UBCRapid/Robin-Platform/Documentation/System diagram.PNG

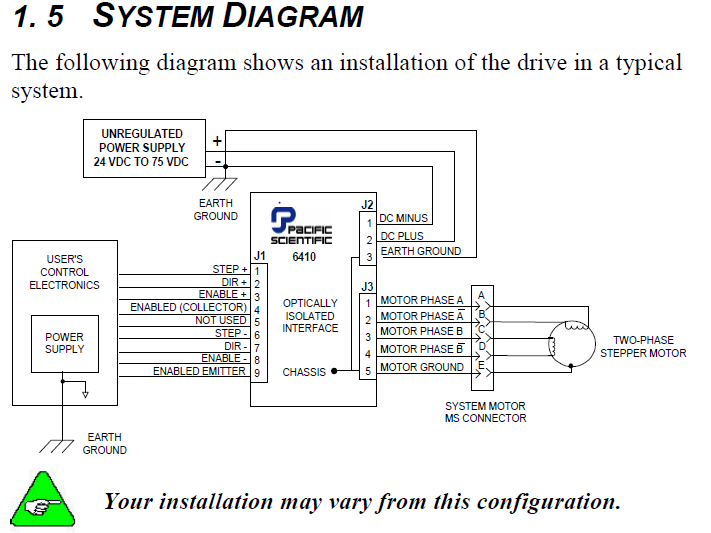
Documentation/System diagram.PNG
