UBCRapid/Robin-Platform/Encoder and Limit Pics/IMG_20140217_170500.jpg

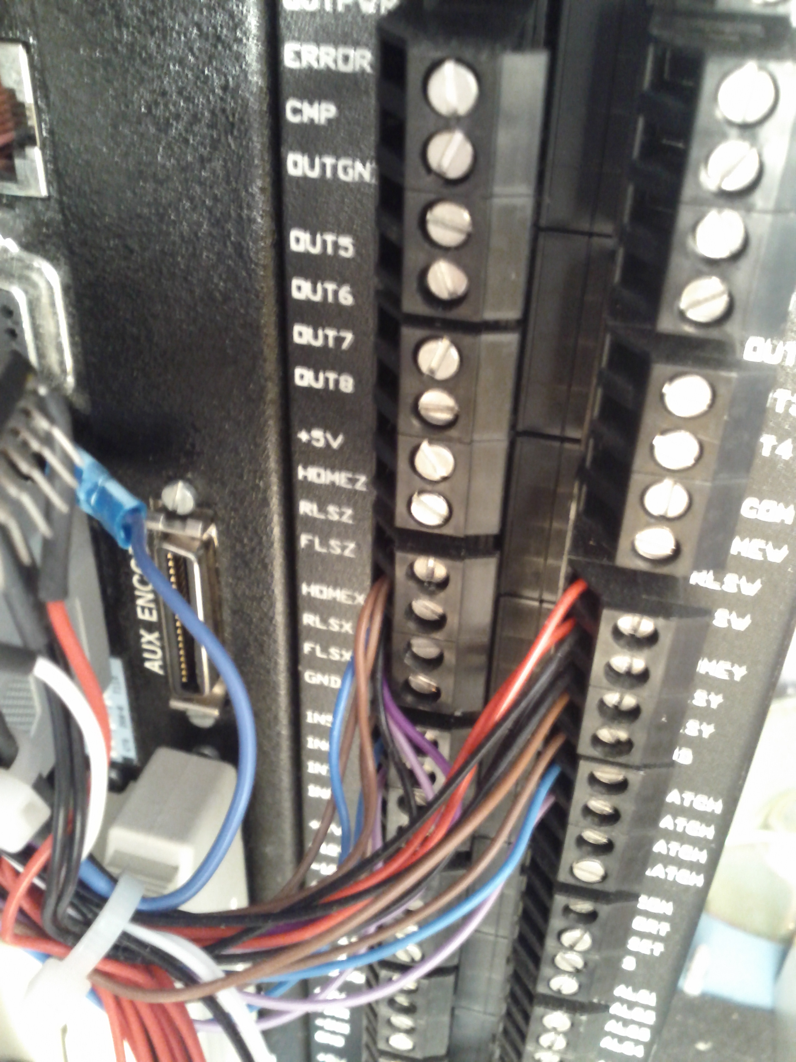
Encoder and Limit Pics/IMG_20140217_170500.jpg
