UBCRapid/Robin-Platform/Encoder and Limit Pics/IMG_20140217_170557.jpg

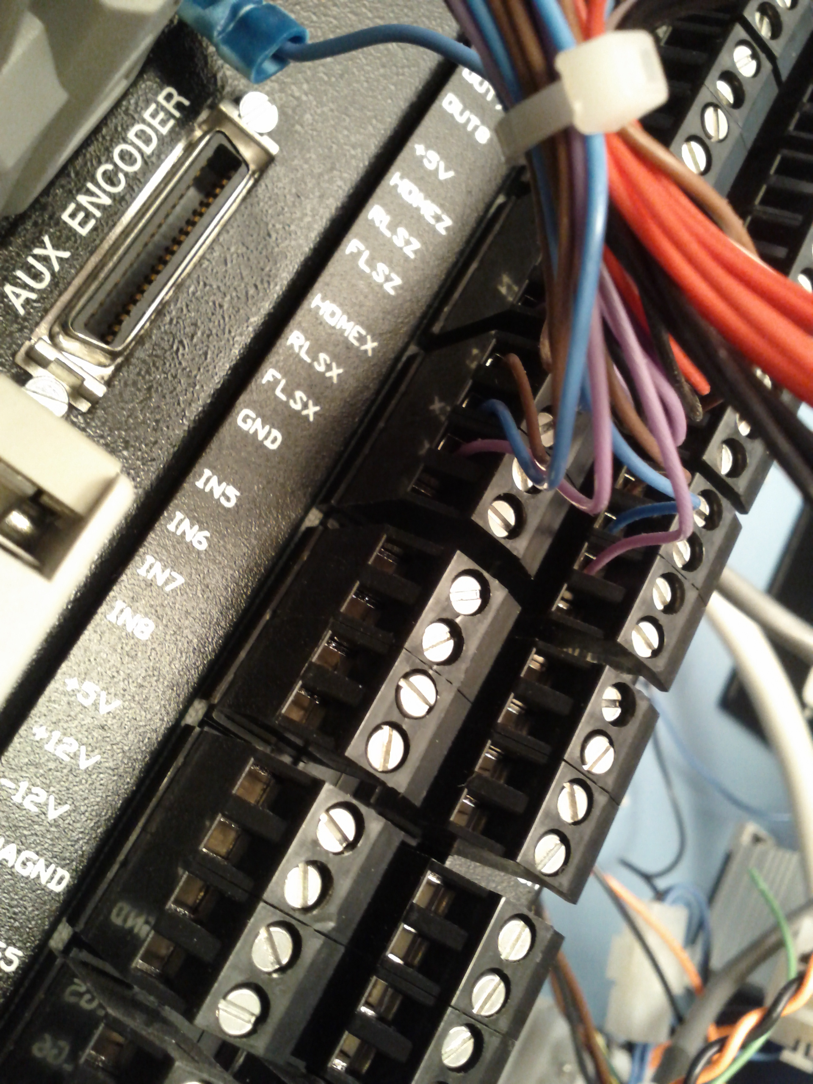
Encoder and Limit Pics/IMG_20140217_170557.jpg
