UBCRapid/Robin-Platform/Encoder and Limit Pics/IMG_20140217_171145.jpg

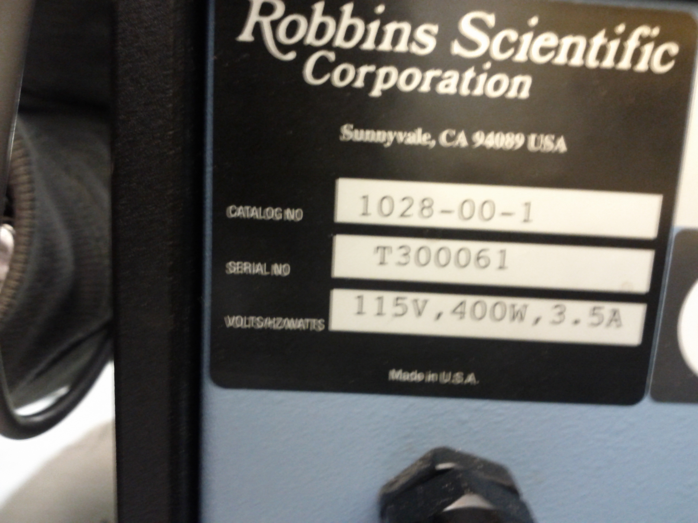
Encoder and Limit Pics/IMG_20140217_171145.jpg
