UBCRapid/Robin-Platform/Solidworks/A0003.sldprt

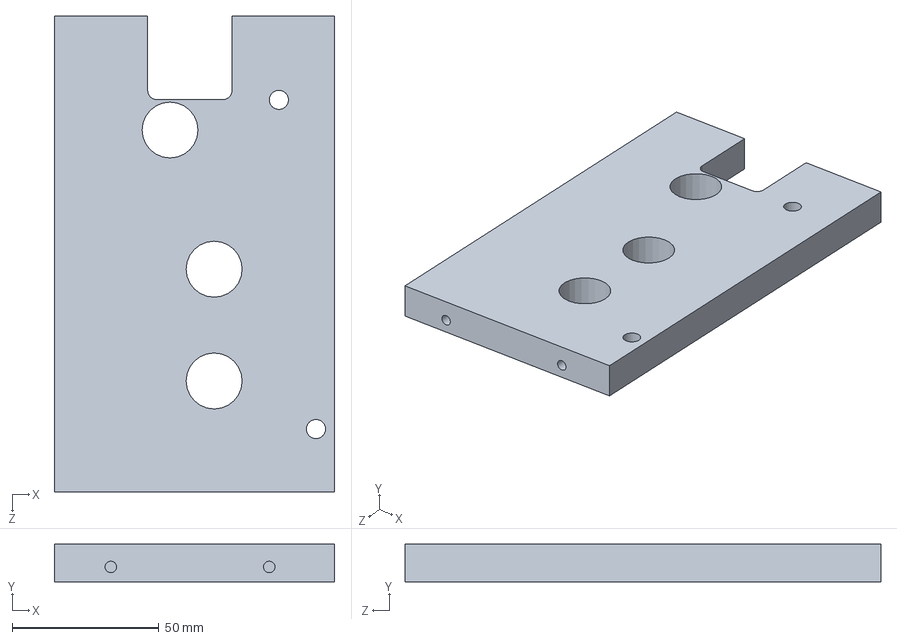
[picture p22: CAD file, 2014-08-17]
Solidworks/A0003.sldprt
95.2 x 12.8 x 161.9 mm
