UBCRapid/Robin-Platform/Solidworks/A0001.SLDPRT

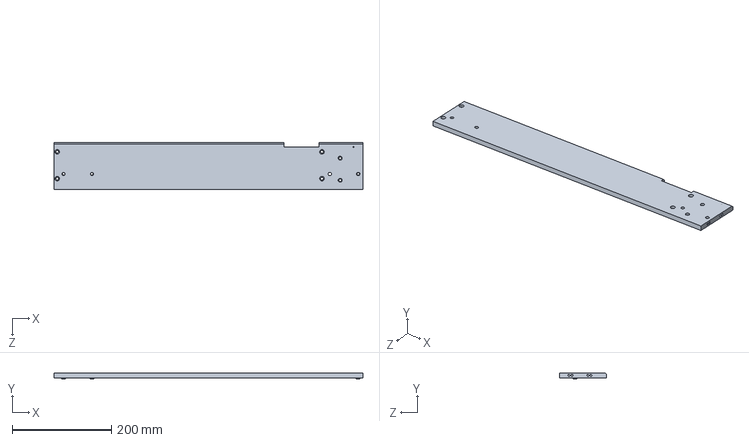
[picture p23: CAD file, 2014-08-17]
Solidworks/A0001.SLDPRT
621.6 x 12.0 x 95.3 mm
