UBCRapid/Robin-Platform/Solidworks/vert_support_plate.SLDPRT

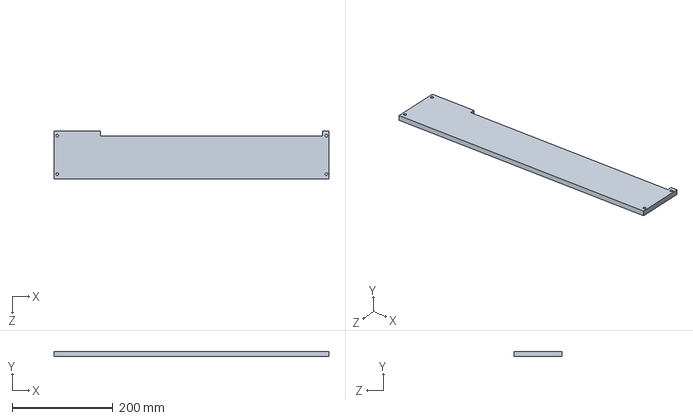
[picture p24: CAD file, 2014-08-17]
Solidworks/vert_support_plate.SLDPRT
545.6 x 9.55 x 95.3 mm
