UBCRapid/Robin-Platform/Solidworks/Front plate.SLDPRT

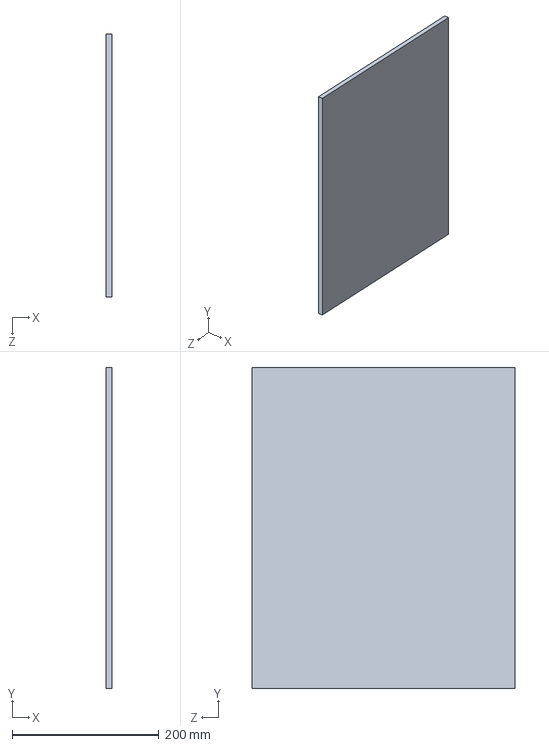
[picture p25: CAD file, 2014-08-17]
Solidworks/Front plate.SLDPRT
8.75 x 438.0 x 359.0 mm
