UBCRapid/Robin-Platform/Solidworks/3-4in_ss_6262K850.SLDPRT

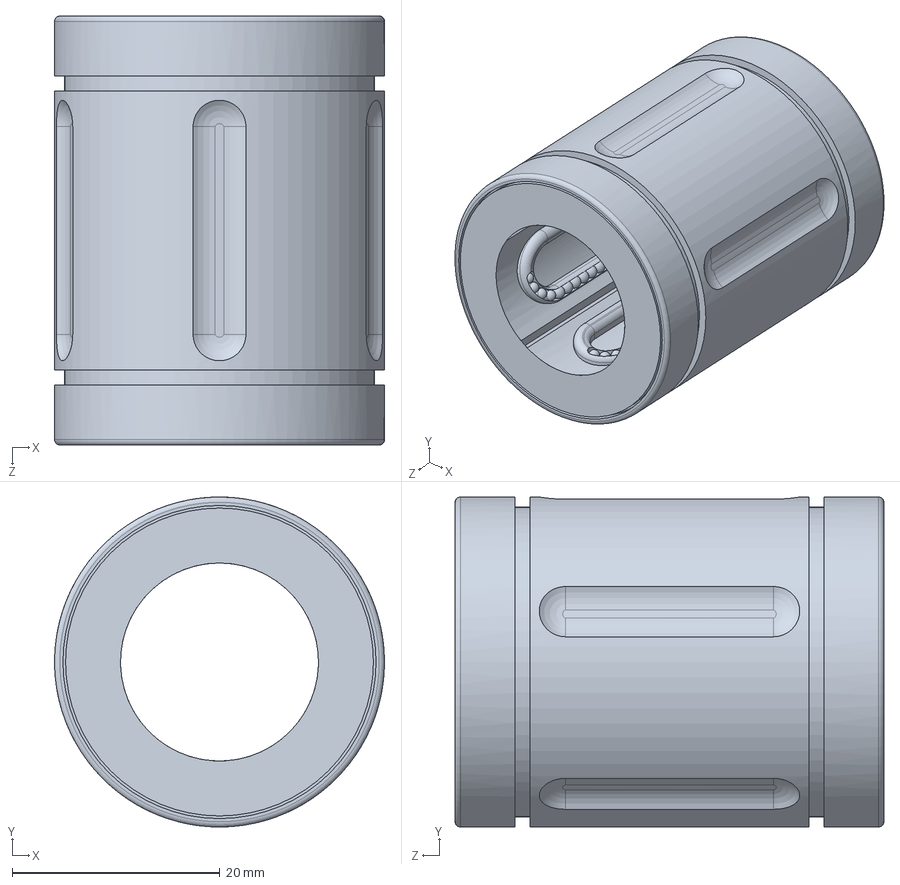
[picture p26: CAD file, 2014-08-17]
Solidworks/3-4in_ss_6262K850.SLDPRT
31.8 x 31.7 x 41.3 mm
