UBCRapid/Robin-Platform/Solidworks/CNC_plate.SLDPRT

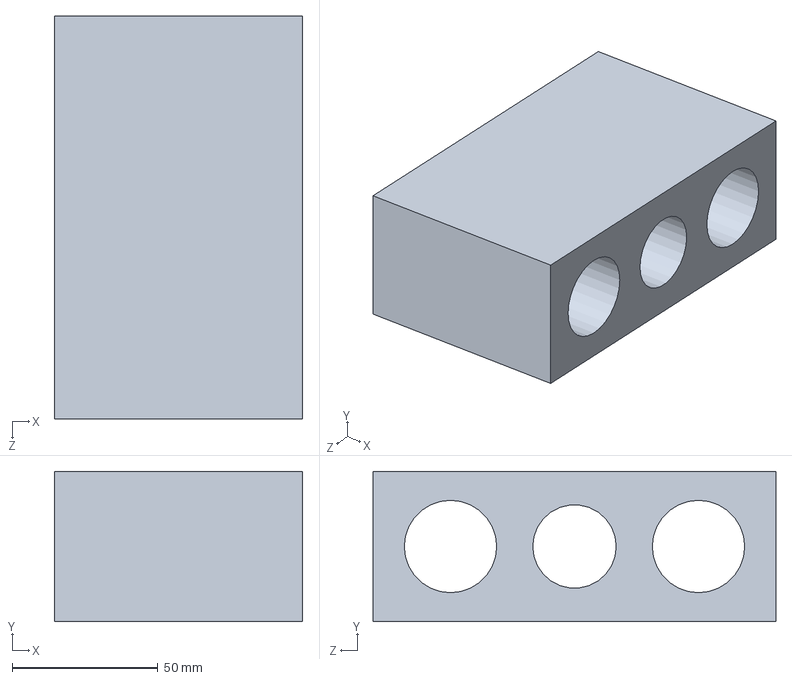
[picture p27: CAD file, 2014-06-20]
Solidworks/CNC_plate.SLDPRT
85.0 x 51.5 x 138.0 mm
