UBCRapid/Robin-Platform/Solidworks/Base.SLDPRT

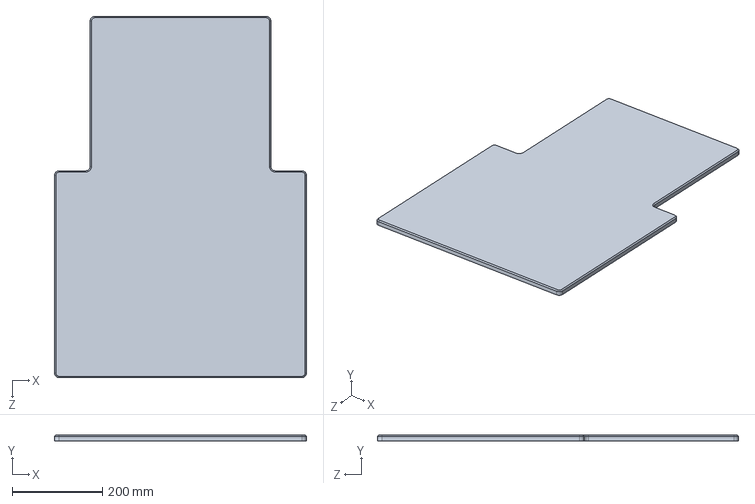
[picture p28: CAD file, 2014-06-12]
Solidworks/Base.SLDPRT
558.0 x 13.0 x 800.0 mm
