UBCRapid/Robin-Platform/Solidworks/bracket.SLDPRT

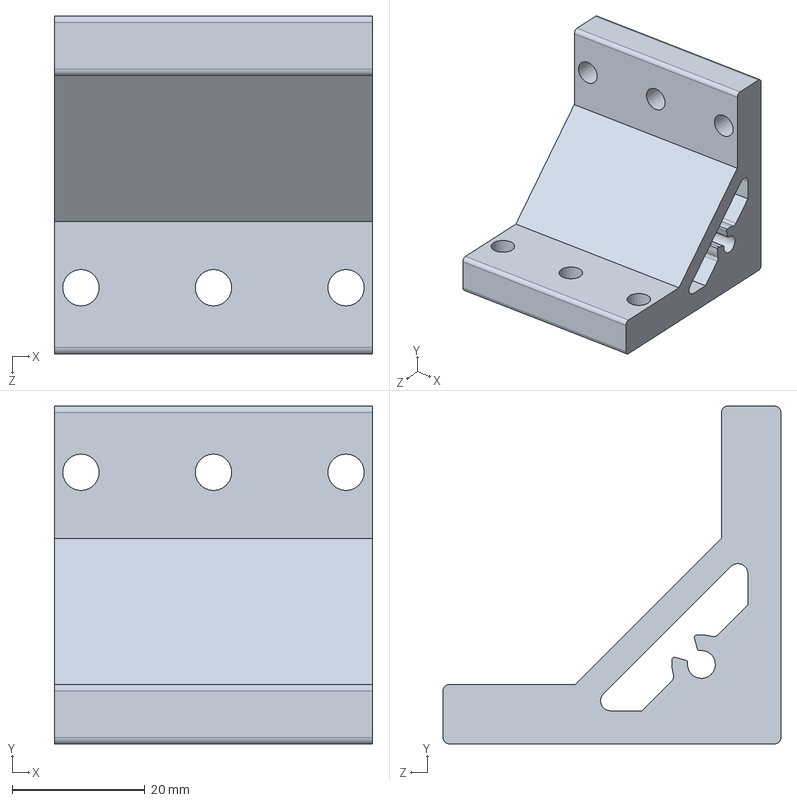
[picture p29: CAD file, 2014-06-12]
Solidworks/bracket.SLDPRT
48.0 x 51.0 x 51.0 mm
