UBCRapid/Robin-Platform/Solidworks/side_piece.SLDPRT

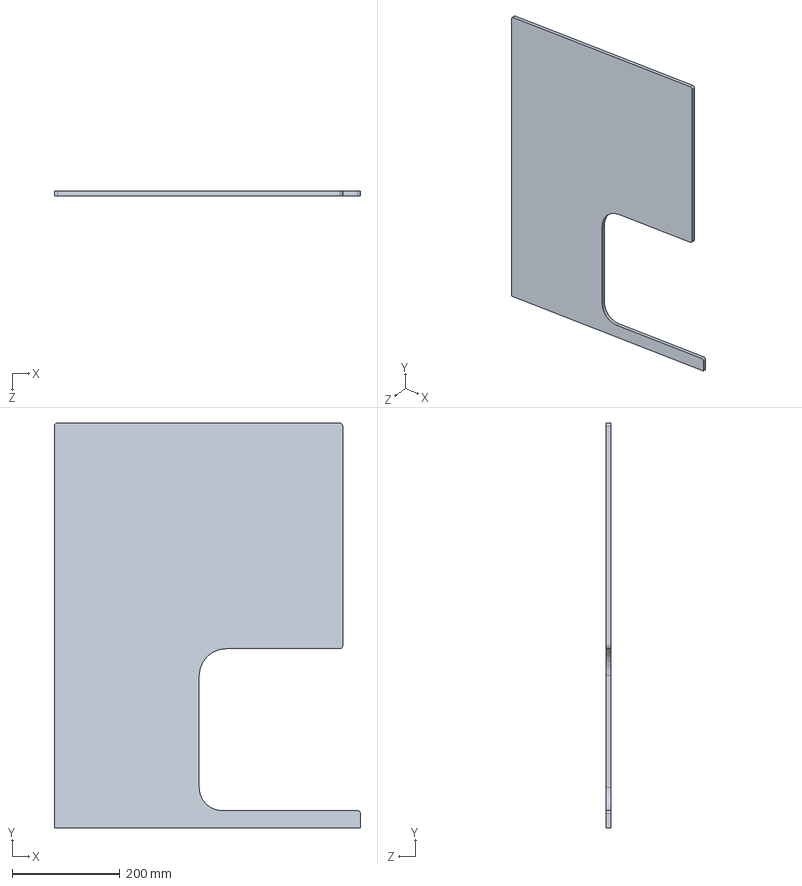
[picture p30: CAD file, 2014-06-12]
Solidworks/side_piece.SLDPRT
567.0 x 750.0 x 8.60 mm
