UBCRapid/Robin-Platform/History/Molecular Bioproducts trademark of Robbins Scientific.PNG

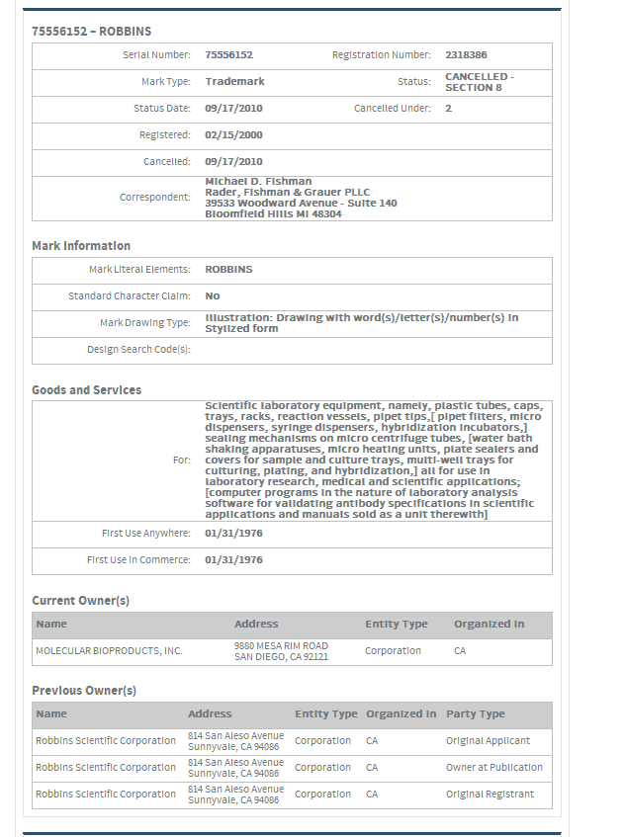
History/Molecular Bioproducts trademark of Robbins Scientific.PNG
