UBCRapid/Robin-Platform/History/News Article from 2003.PNG

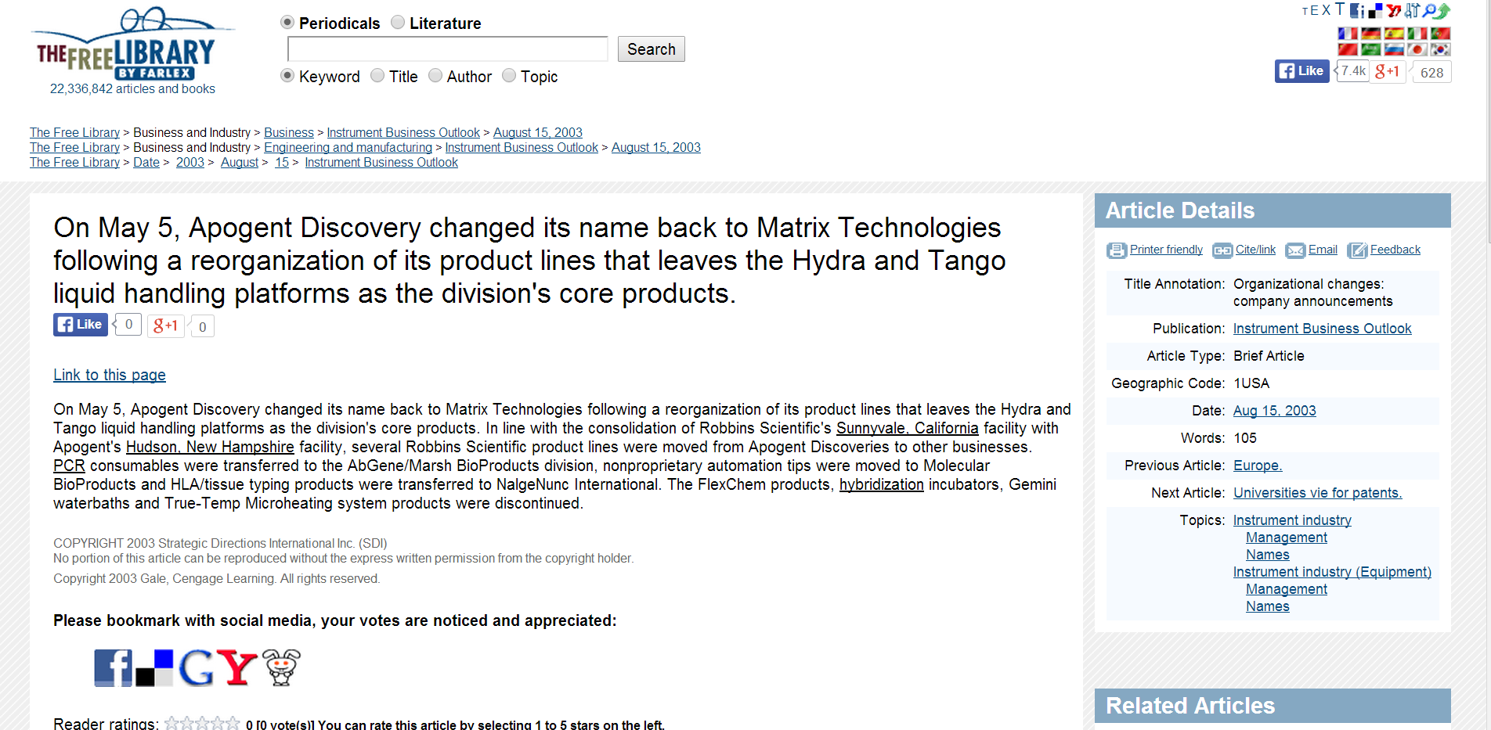
History/News Article from 2003.PNG
