UBCRapid/Robin-Platform/History/Trademarks owned by Molecular Bioproducts.PNG

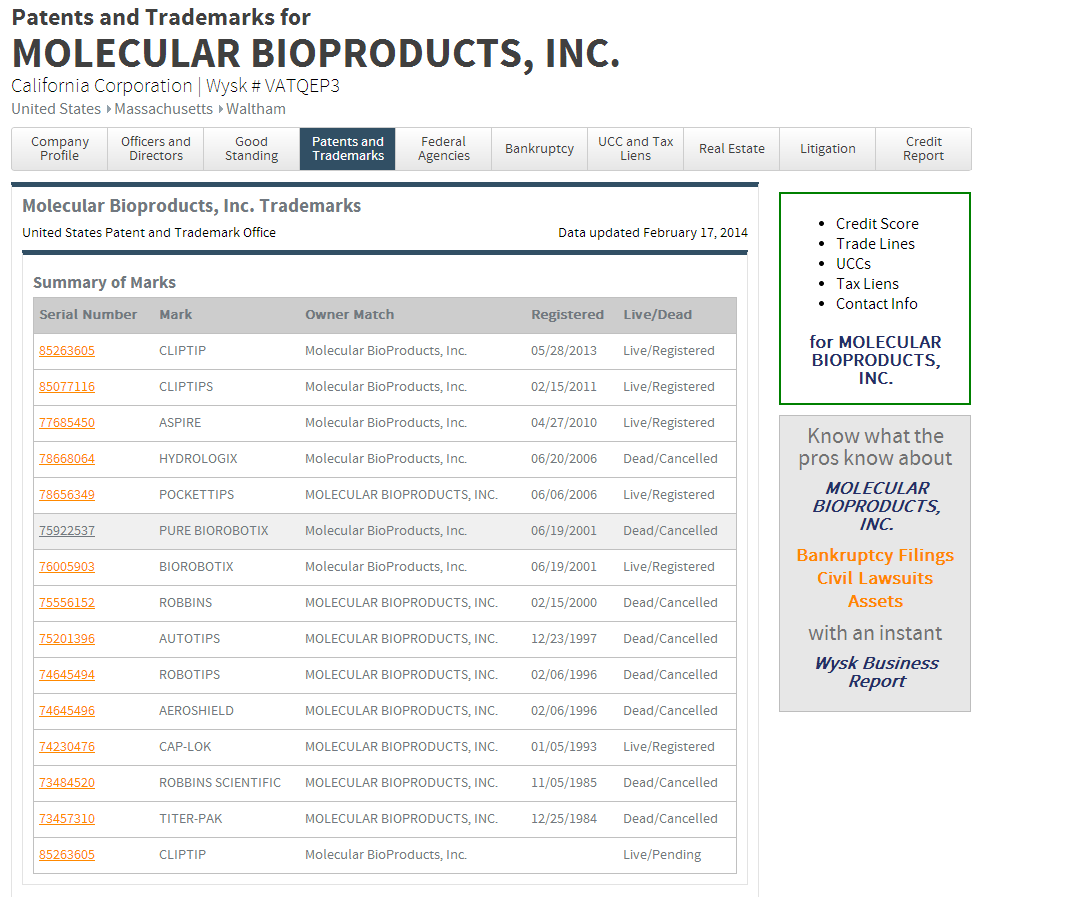
History/Trademarks owned by Molecular Bioproducts.PNG
